grodansparadis/can4vscp-frankfurt-eth/images/frankfurt_esp32_eth_rev_a_back.png

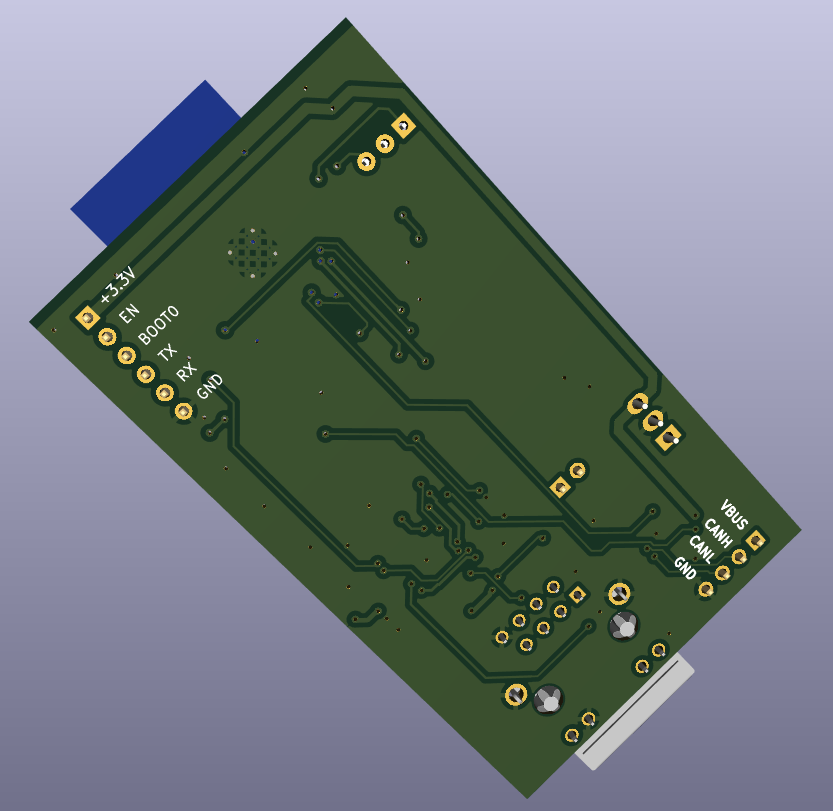
images/frankfurt_esp32_eth_rev_a_back.png
