grodansparadis/can4vscp-frankfurt-eth/pic-version/docs/324465907_o.jpg

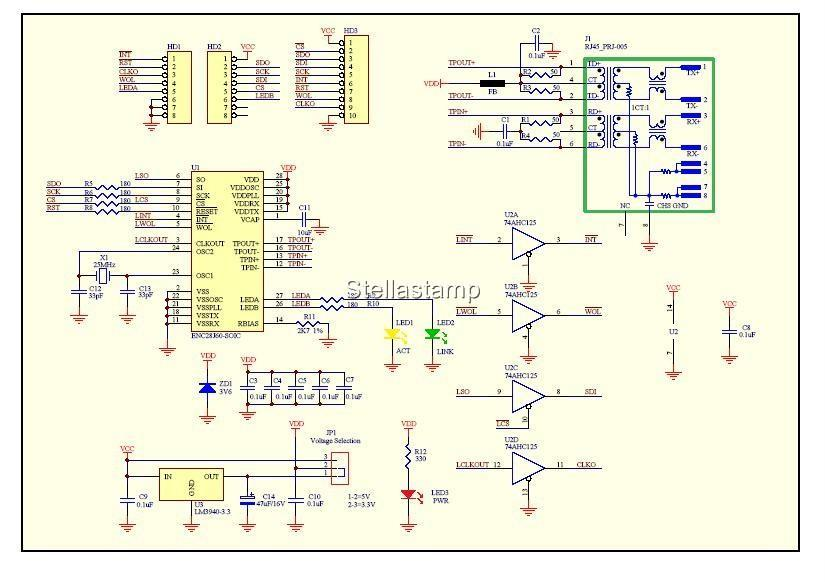
pic-version/docs/324465907_o.jpg
