grodansparadis/can4vscp-frankfurt-eth/pic-version/docs/20119212230409.gif

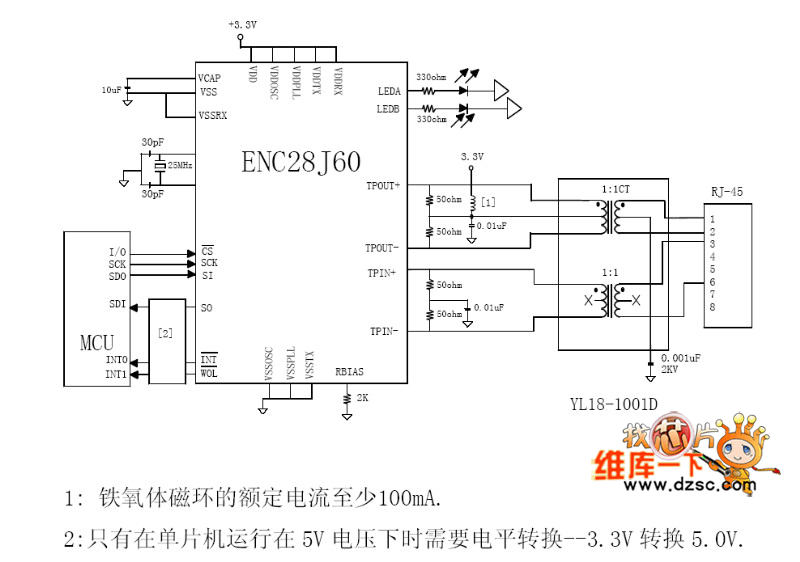
pic-version/docs/20119212230409.gif
