grodansparadis/can4vscp-frankfurt-eth/pic-version/docs/ethernet_scb.gif

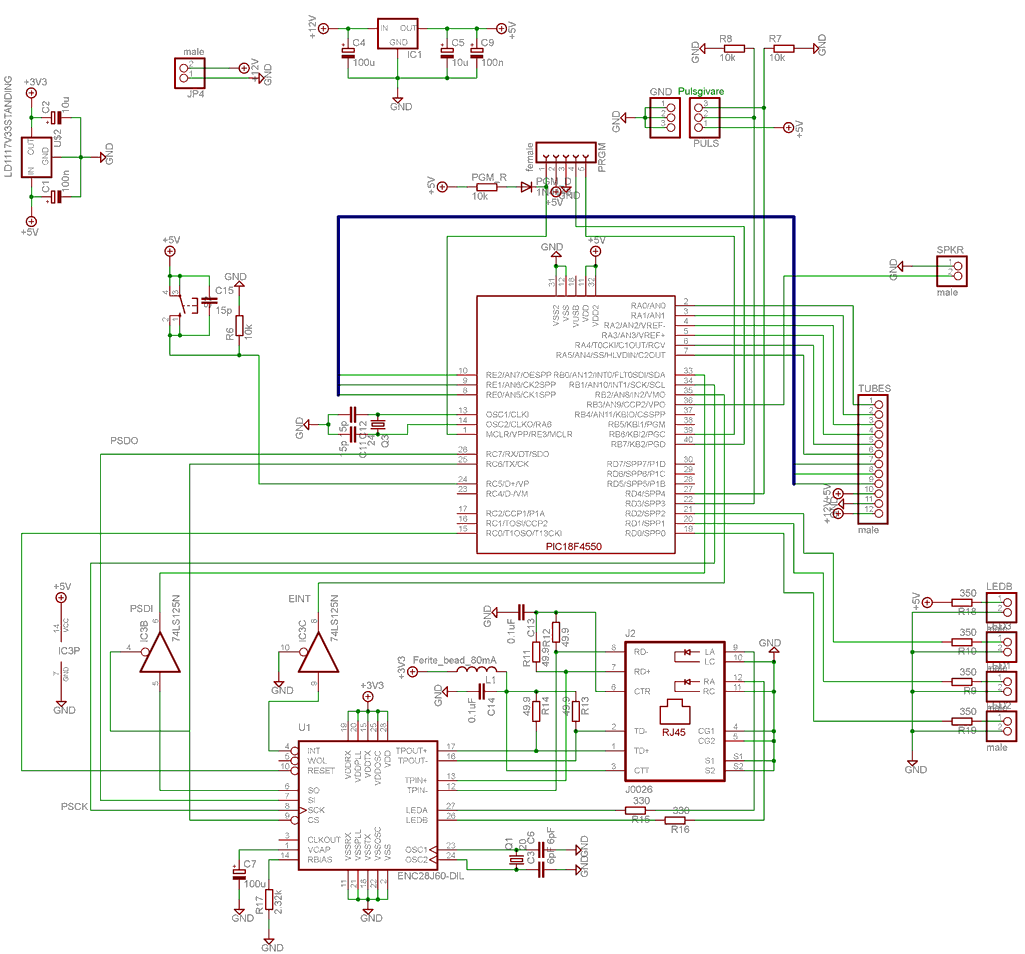
pic-version/docs/ethernet_scb.gif
