grodansparadis/can4vscp-frankfurt-eth/pic-version/docs/schema_ds.gif

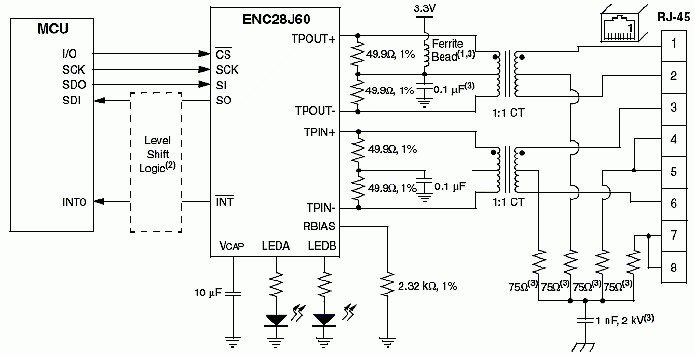
pic-version/docs/schema_ds.gif
