grodansparadis/can4vscp-frankfurt-eth/pic-version/docs/scheme_spi_ethernet2.gif

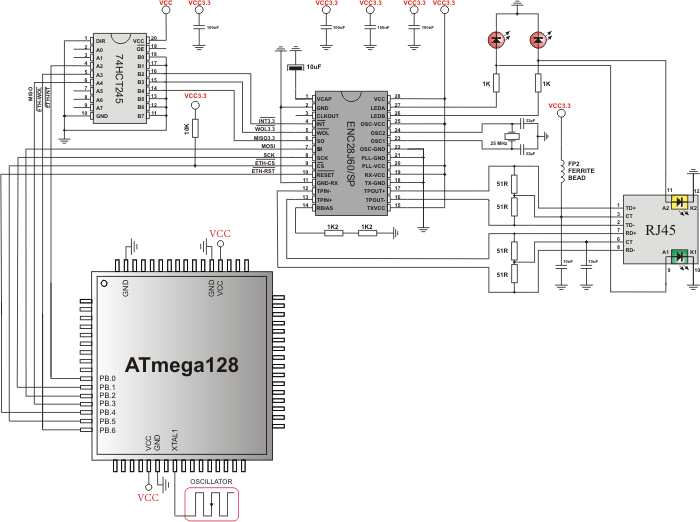
pic-version/docs/scheme_spi_ethernet2.gif
