grodansparadis/can4vscp-frankfurt-eth/pic-version/docs/stu4U.png

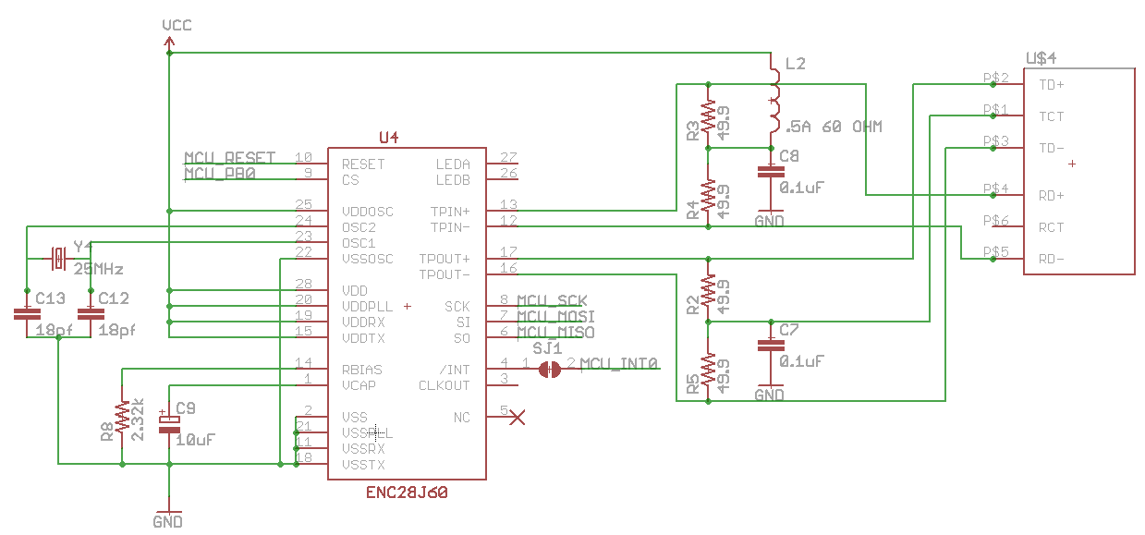
pic-version/docs/stu4U.png
