grodansparadis/can4vscp-frankfurt-eth/pic-version/eagle/frankfurt_eth_arm_rev_a_sch3.png

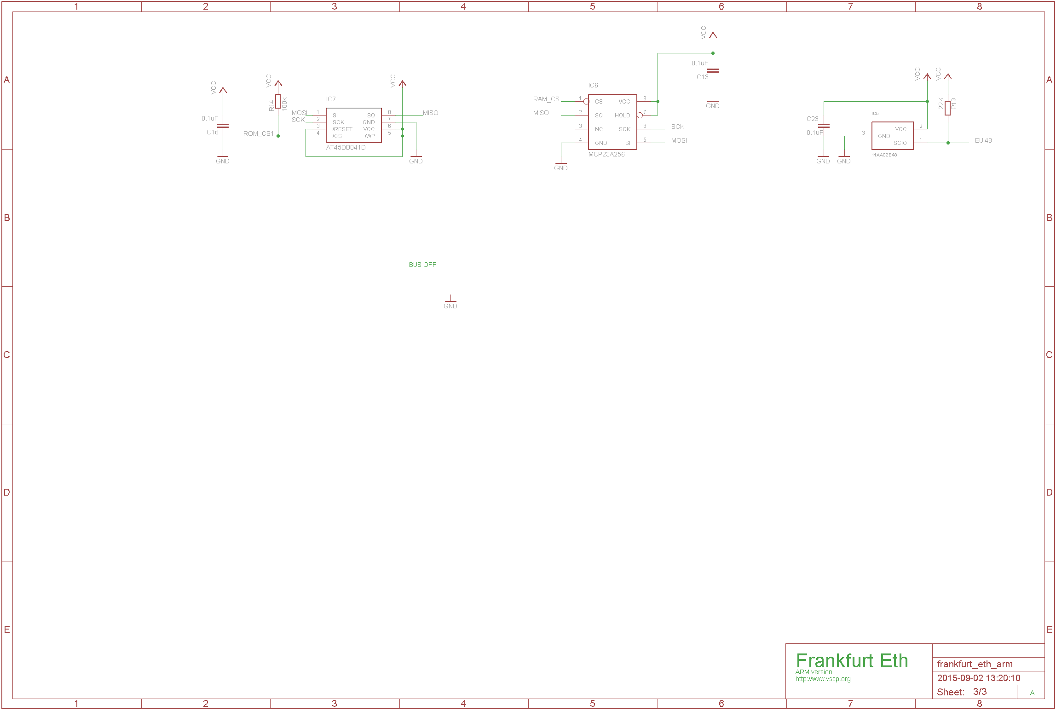
pic-version/eagle/frankfurt_eth_arm_rev_a_sch3.png
