grodansparadis/can4vscp-frankfurt-eth/pic-version/eagle/frankfurt_eth_pic_rev_a_brd.png

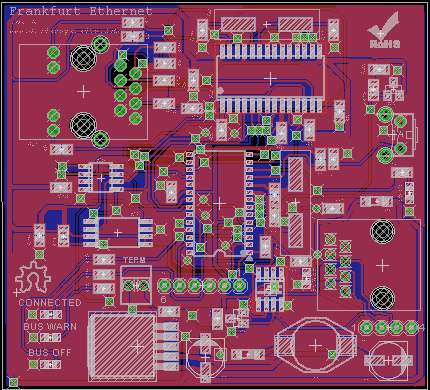
pic-version/eagle/frankfurt_eth_pic_rev_a_brd.png
