grodansparadis/can4vscp-frankfurt-eth/pic-version/eagle/frankfurt_eth_pic_rev_a_sch1.png

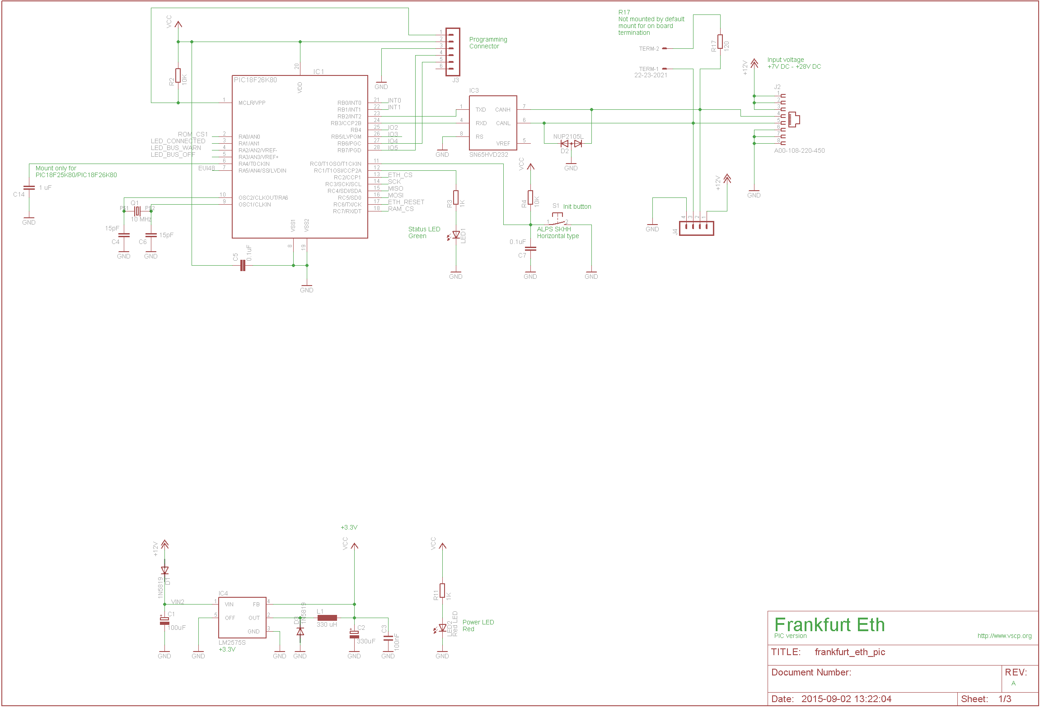
pic-version/eagle/frankfurt_eth_pic_rev_a_sch1.png
