grodansparadis/can4vscp-frankfurt-eth/pic-version/eagle/Gerbers/pic/frankfurt_eth_pic_gerbers_150925_gbs_small.png

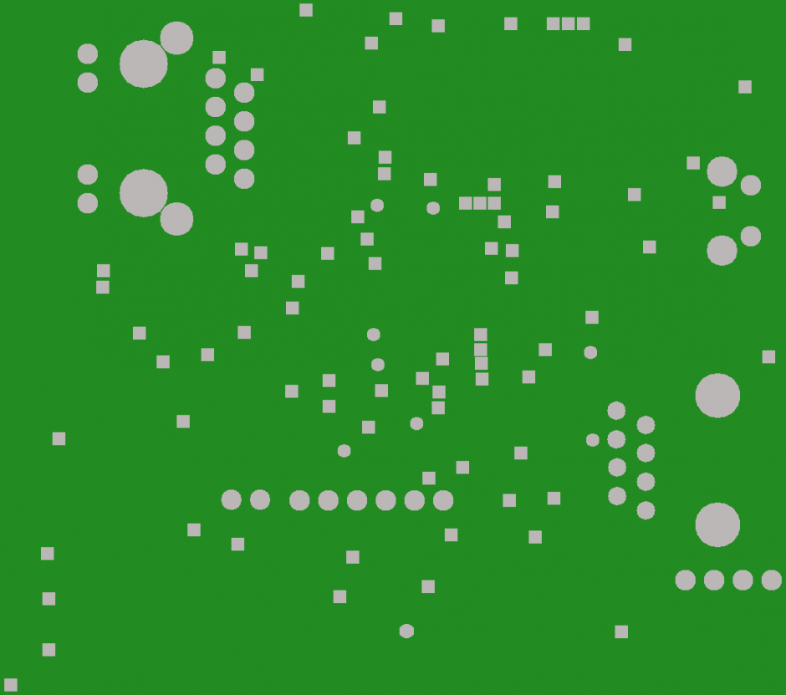
pic-version/eagle/Gerbers/pic/frankfurt_eth_pic_gerbers_150925_gbs_small.png
